Blyzz616/the-nut/gifs/01.gif

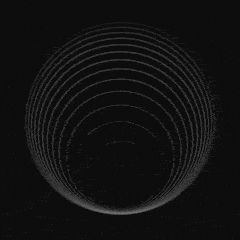
gifs/01.gif
