Blyzz616/the-nut/gifs/02.gif

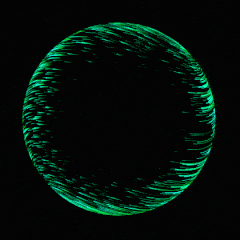
gifs/02.gif
