Blyzz616/the-nut/gifs/03.gif

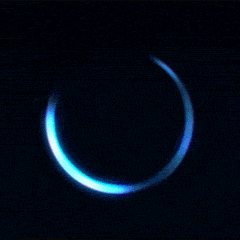
gifs/03.gif
