Blyzz616/the-nut/gifs/05.gif

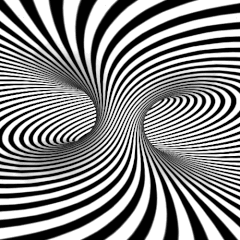
gifs/05.gif
