Blyzz616/the-nut/gifs/06.gif

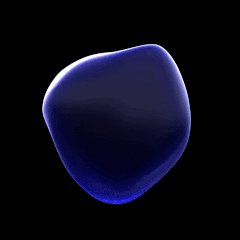
gifs/06.gif
