Blyzz616/the-nut/gifs/07.gif

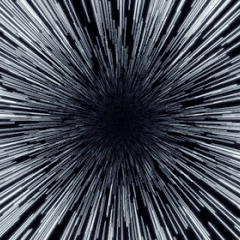
gifs/07.gif
