Blyzz616/the-nut/gifs/08.gif

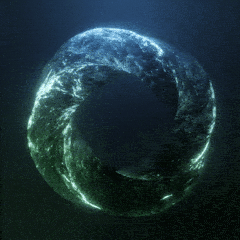
gifs/08.gif
