Blyzz616/the-nut/gifs/10.gif

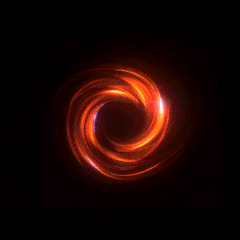
gifs/10.gif
