Blyzz616/the-nut/gifs/11.gif

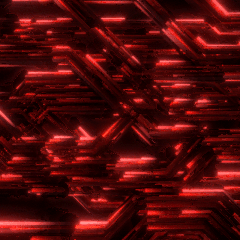
gifs/11.gif
