Blyzz616/the-nut/gifs/12.gif

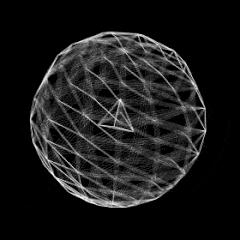
gifs/12.gif
